ouaguenouni/Matrix-Studio-ESP32/cad/enclosure-comparison/01-line/exploded.png

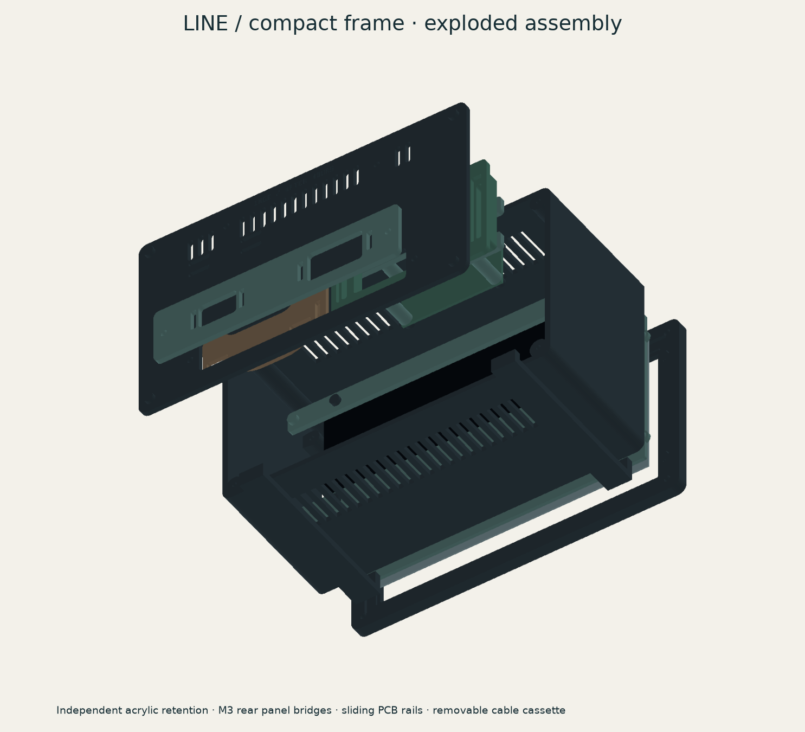
cad/enclosure-comparison/01-line/exploded.png
