ouaguenouni/Matrix-Studio-ESP32/cad/enclosure-comparison/03-gallery/exploded.png

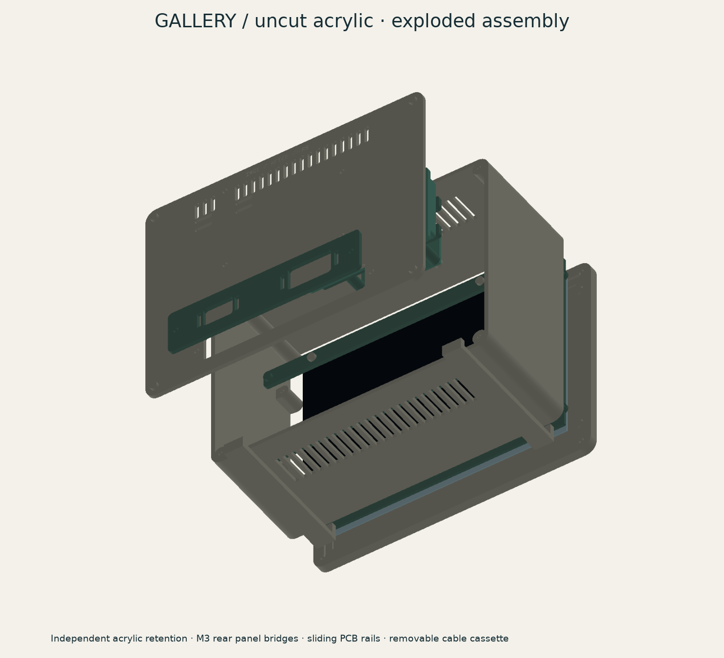
cad/enclosure-comparison/03-gallery/exploded.png
