ouaguenouni/Matrix-Studio-ESP32/cad/enclosure-comparison/04-vault/exploded.png

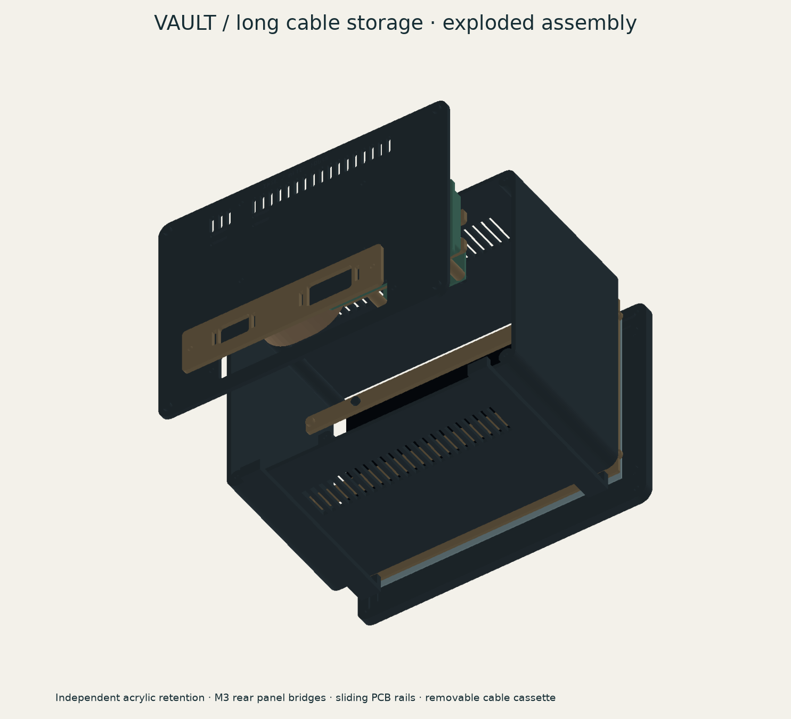
cad/enclosure-comparison/04-vault/exploded.png
