ouaguenouni/Matrix-Studio-ESP32/cad/enclosure-comparison/04-vault/preview.png

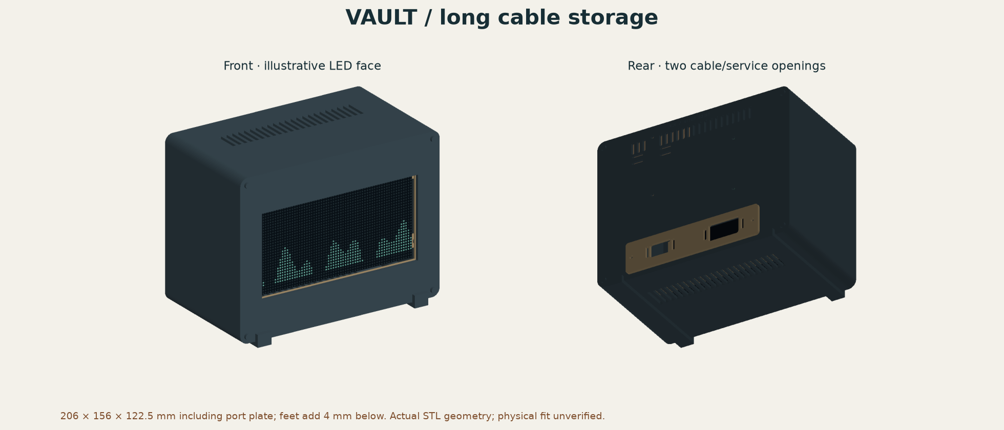
cad/enclosure-comparison/04-vault/preview.png
