ouaguenouni/Matrix-Studio-ESP32/cad/enclosure-comparison/vault-service.png

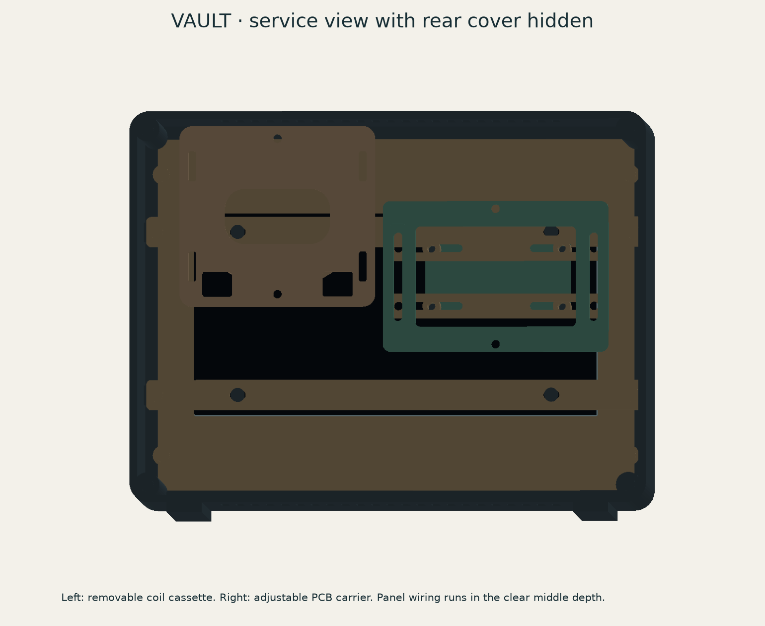
cad/enclosure-comparison/vault-service.png
