ouaguenouni/Matrix-Studio-ESP32/pictures/IMG_20261005_003129984.jpg

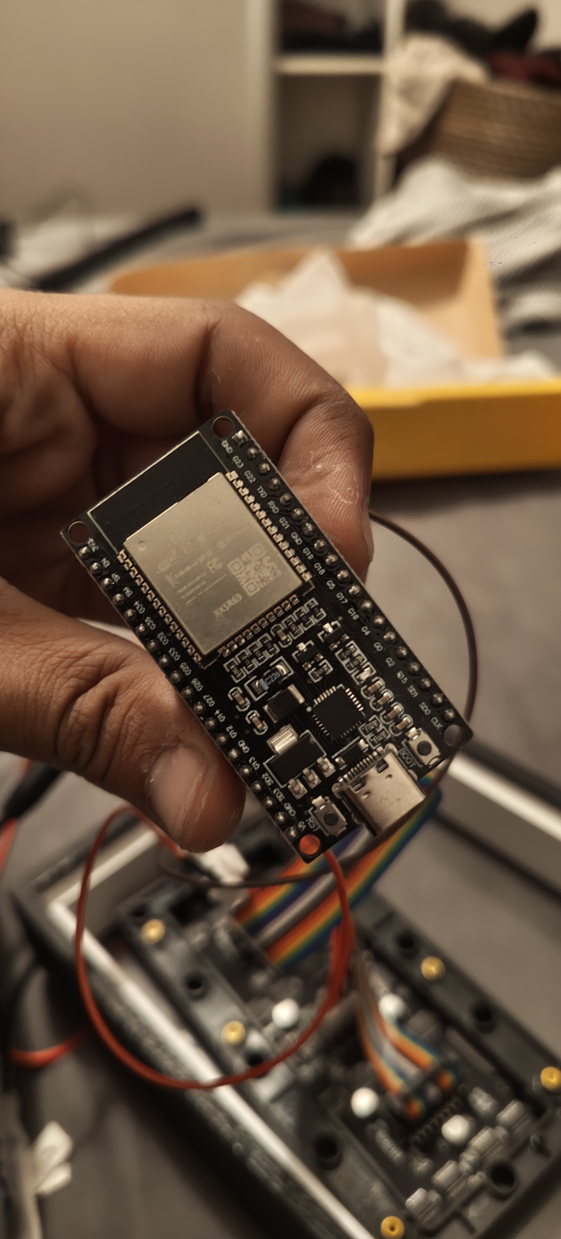
pictures/IMG_20261005_003129984.jpg
