ouaguenouni/Matrix-Studio-ESP32/pictures/IMG_20261005_003135957.jpg

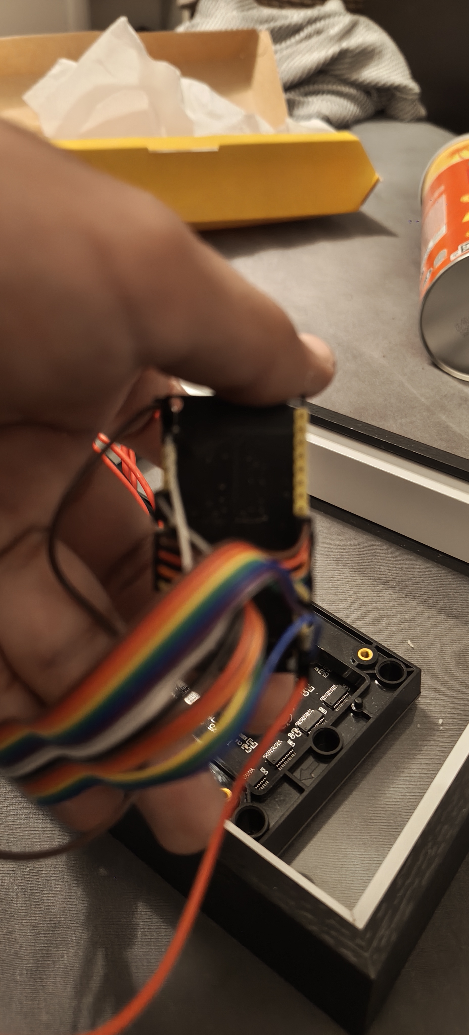
pictures/IMG_20261005_003135957.jpg
