ouaguenouni/Matrix-Studio-ESP32/pictures/IMG_20261005_003139460.jpg

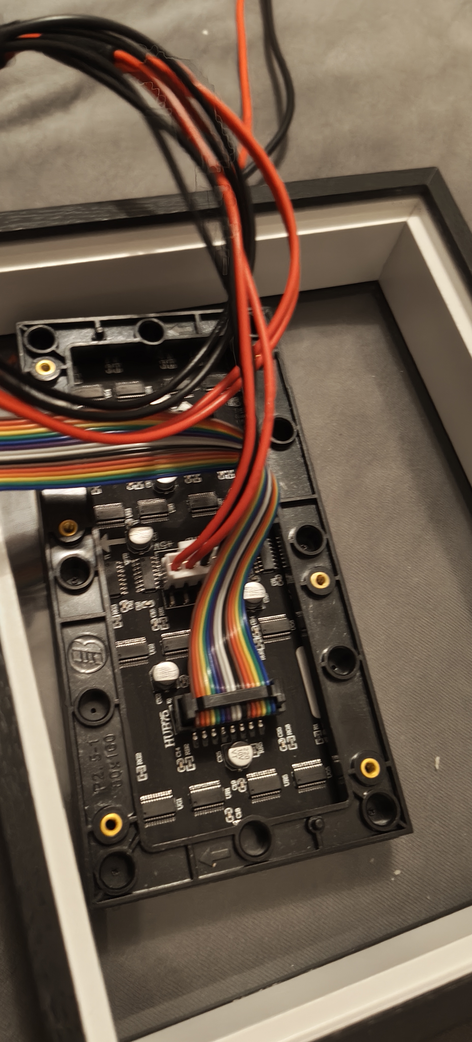
pictures/IMG_20261005_003139460.jpg
