ouaguenouni/Matrix-Studio-ESP32/pictures/IMG_20261005_003144986.jpg

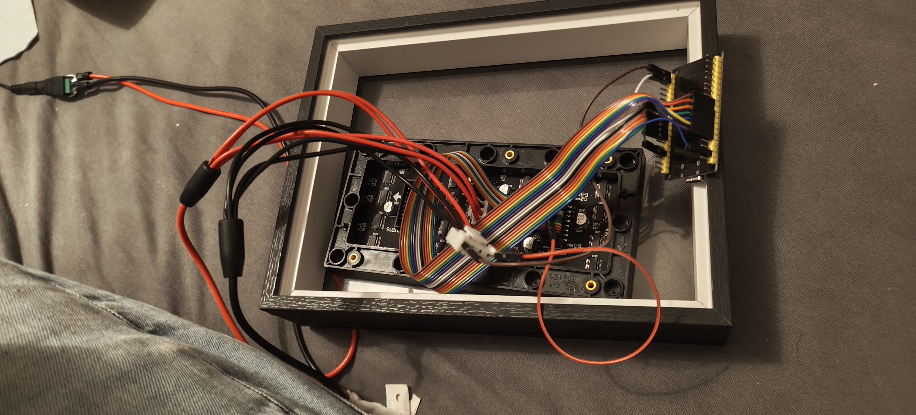
pictures/IMG_20261005_003144986.jpg
