ouaguenouni/Matrix-Studio-ESP32/pictures/IMG_20261005_003153289.jpg

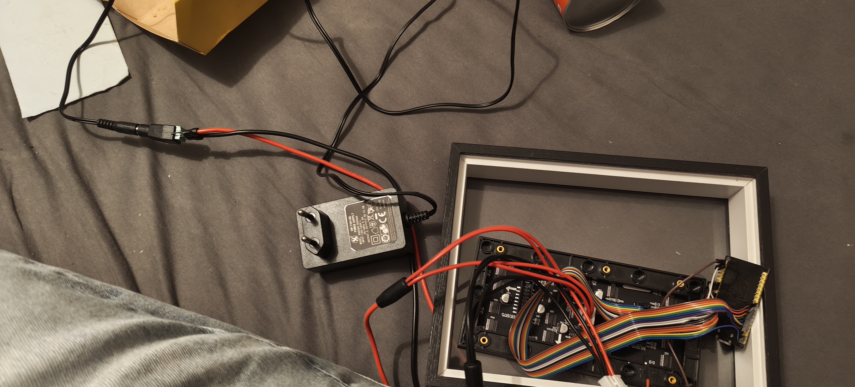
pictures/IMG_20261005_003153289.jpg
