ouaguenouni/Matrix-Studio-ESP32/cad/enclosure-comparison/01-line/stl/carrier.stl

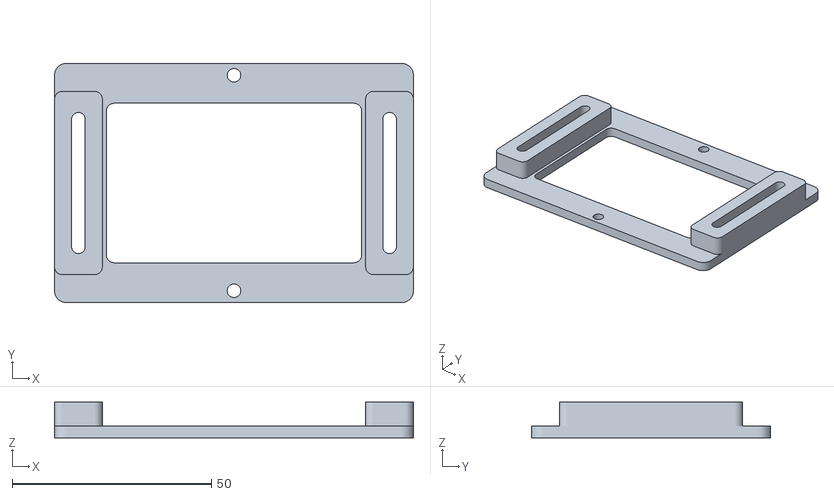
[picture p32: CAD file, 2026-10-05]
cad/enclosure-comparison/01-line/stl/carrier.stl
90.0 x 60.0 x 9.00
