ouaguenouni/Matrix-Studio-ESP32/cad/enclosure-comparison/03-gallery/stl/body.stl

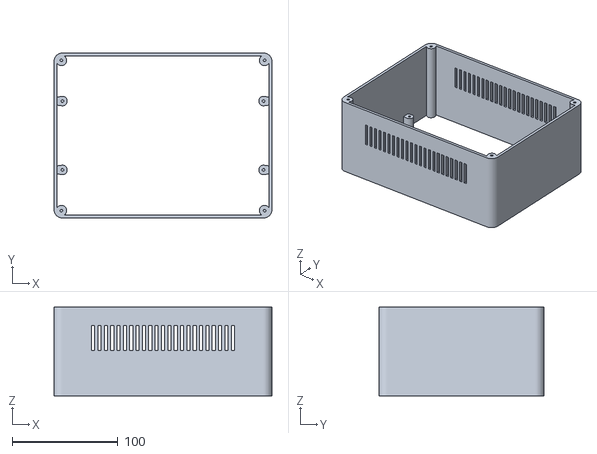
[picture p33: CAD file, 2026-10-05]
cad/enclosure-comparison/03-gallery/stl/body.stl
206.0 x 156.0 x 84.0
