ouaguenouni/Matrix-Studio-ESP32/cad/enclosure-comparison/04-vault/stl/body.stl

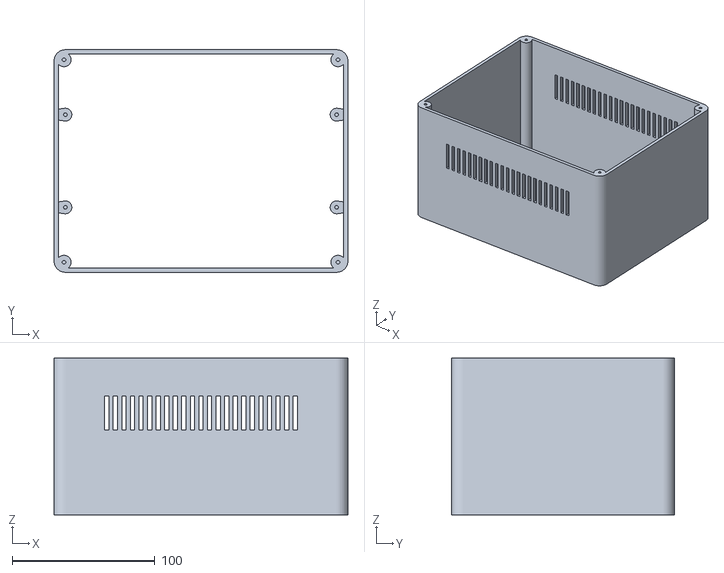
[picture p34: CAD file, 2026-10-05]
cad/enclosure-comparison/04-vault/stl/body.stl
206.0 x 156.0 x 110.0
