ouaguenouni/Matrix-Studio-ESP32/cad/enclosure-comparison/05-console/stl/keeper.stl

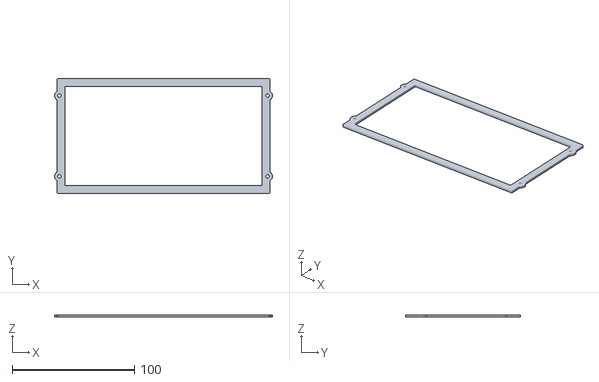
[picture p35: CAD file, 2026-10-05]
cad/enclosure-comparison/05-console/stl/keeper.stl
178.0 x 94.0 x 2.00
