ouaguenouni/Matrix-Studio-ESP32/cad/inge-after-hours/prototype-stl/lid.stl

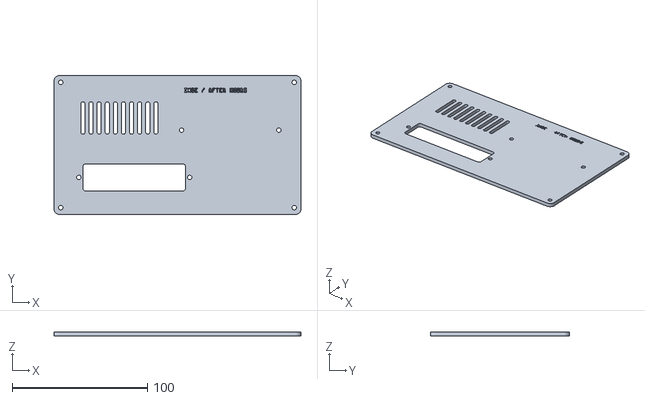
[picture p36: CAD file, 2026-10-05]
cad/inge-after-hours/prototype-stl/lid.stl
182.8 x 102.8 x 3.00
