ouaguenouni/Matrix-Studio-ESP32/cad/minimal-frame/reference/power_mock.stl

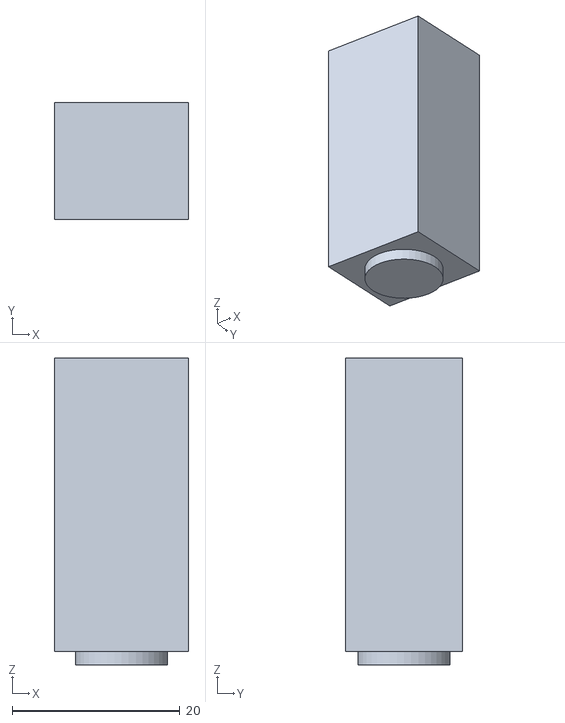
[picture p37: CAD file, 2026-10-05]
cad/minimal-frame/reference/power_mock.stl
16.0 x 14.0 x 36.6
