ouaguenouni/Matrix-Studio-ESP32/cad/enclosure-comparison/01-line/stl/ports.stl

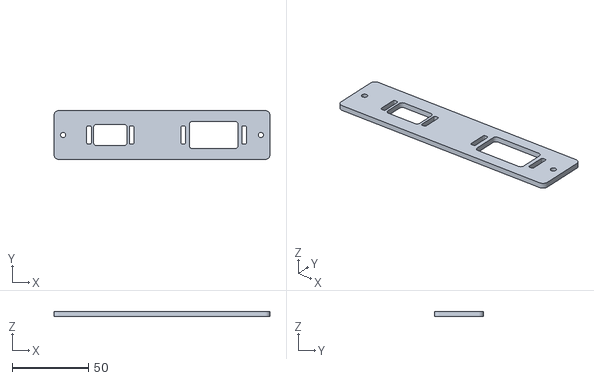
[picture p38: CAD file, 2026-10-05]
cad/enclosure-comparison/01-line/stl/ports.stl
142.0 x 32.0 x 3.00
