ouaguenouni/Matrix-Studio-ESP32/cad/enclosure-comparison/02-orbit/stl/spacer.stl

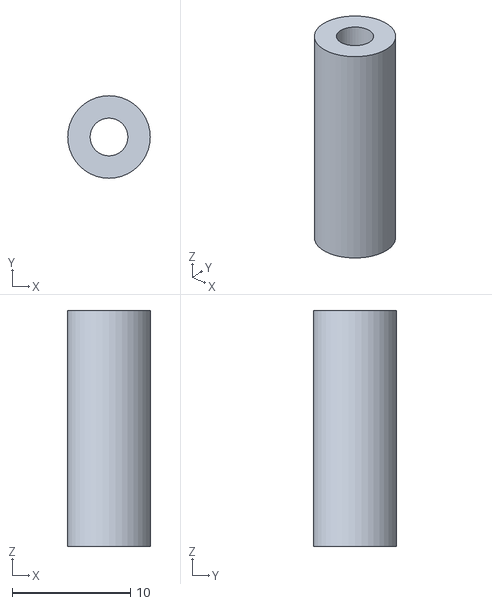
[picture p39: CAD file, 2026-10-05]
cad/enclosure-comparison/02-orbit/stl/spacer.stl
7.00 x 7.00 x 20.0
