ouaguenouni/Matrix-Studio-ESP32/cad/enclosure-comparison/03-gallery/stl/bridge.stl

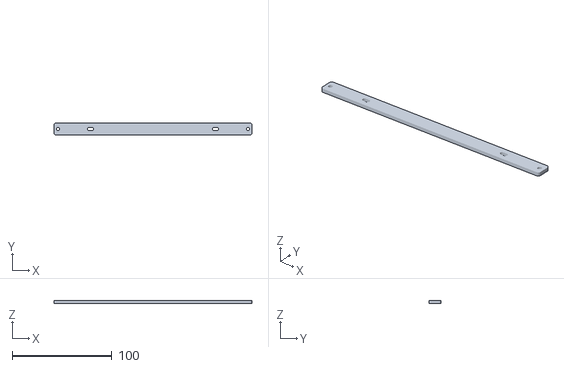
[picture p40: CAD file, 2026-10-05]
cad/enclosure-comparison/03-gallery/stl/bridge.stl
198.0 x 12.0 x 3.00
