ouaguenouni/Matrix-Studio-ESP32/cad/inge-after-hours/prototype-stl/carrier.stl

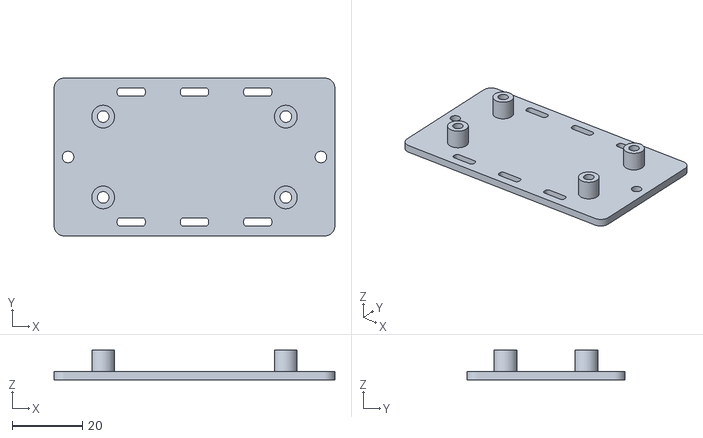
[picture p41: CAD file, 2026-10-05]
cad/inge-after-hours/prototype-stl/carrier.stl
80.0 x 45.0 x 8.40
