ouaguenouni/Matrix-Studio-ESP32/cad/minimal-frame/reference/usb_mock.stl

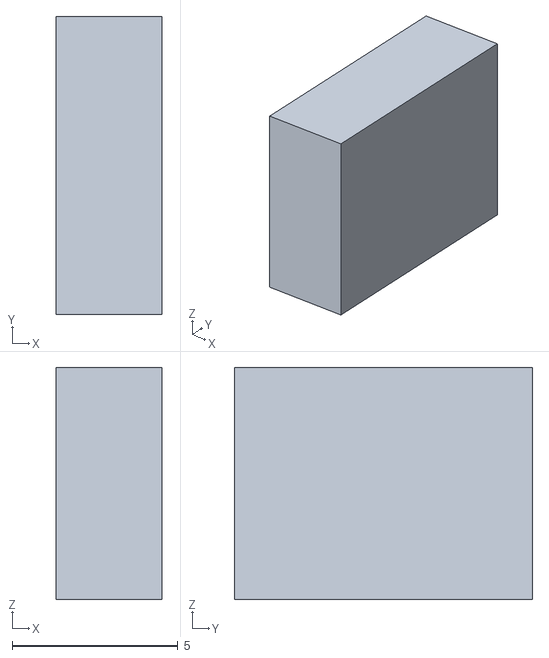
[picture p42: CAD file, 2026-10-05]
cad/minimal-frame/reference/usb_mock.stl
3.20 x 9.00 x 7.00
