ouaguenouni/Matrix-Studio-ESP32/cad/enclosure-comparison/01-line/stl/rail.stl

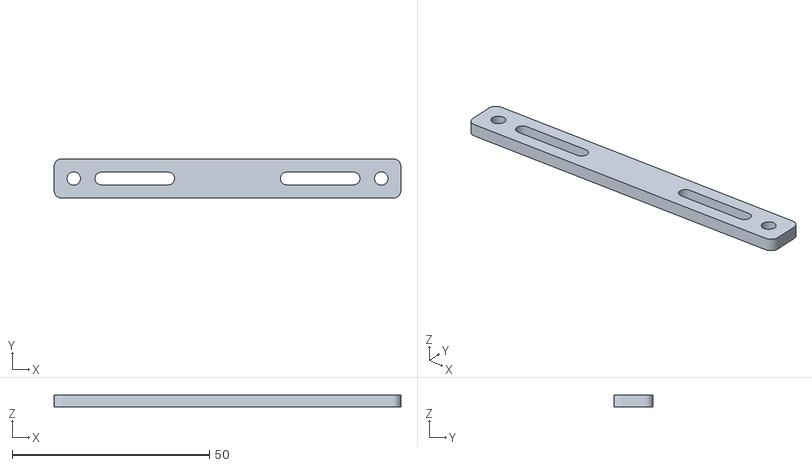
[picture p43: CAD file, 2026-10-05]
cad/enclosure-comparison/01-line/stl/rail.stl
88.0 x 10.0 x 3.00
