ouaguenouni/Matrix-Studio-ESP32/cad/enclosure-comparison/02-orbit/stl/body.stl

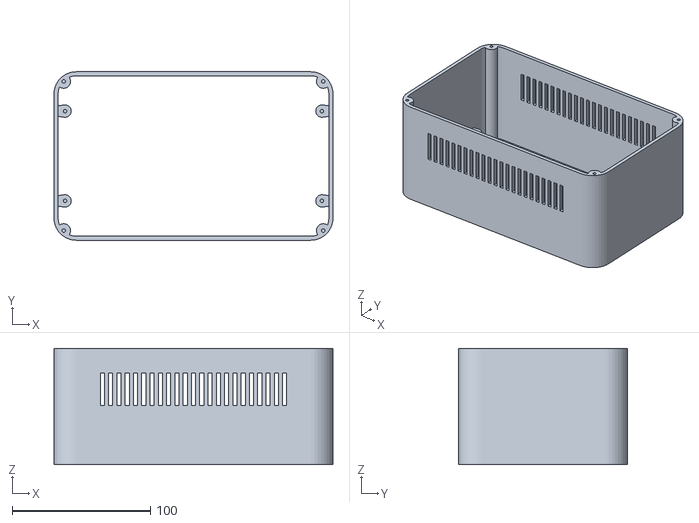
[picture p44: CAD file, 2026-10-05]
cad/enclosure-comparison/02-orbit/stl/body.stl
202.0 x 122.0 x 84.0
