ouaguenouni/Matrix-Studio-ESP32/cad/enclosure-comparison/03-gallery/stl/keeper.stl

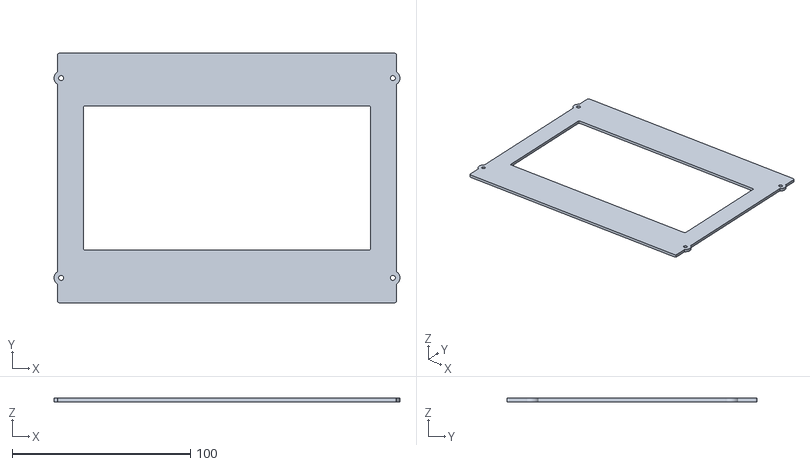
[picture p45: CAD file, 2026-10-05]
cad/enclosure-comparison/03-gallery/stl/keeper.stl
194.0 x 140.0 x 2.00
