ouaguenouni/Matrix-Studio-ESP32/cad/enclosure-comparison/04-vault/stl/feet.stl

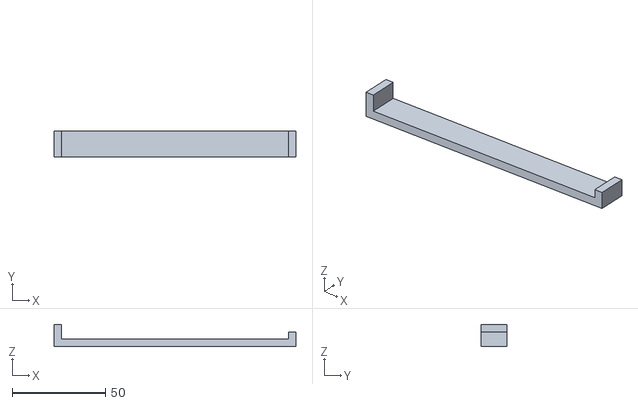
[picture p46: CAD file, 2026-10-05]
cad/enclosure-comparison/04-vault/stl/feet.stl
129.5 x 14.0 x 12.0
