ouaguenouni/Matrix-Studio-ESP32/cad/inge-after-hours/prototype-stl/stand.stl

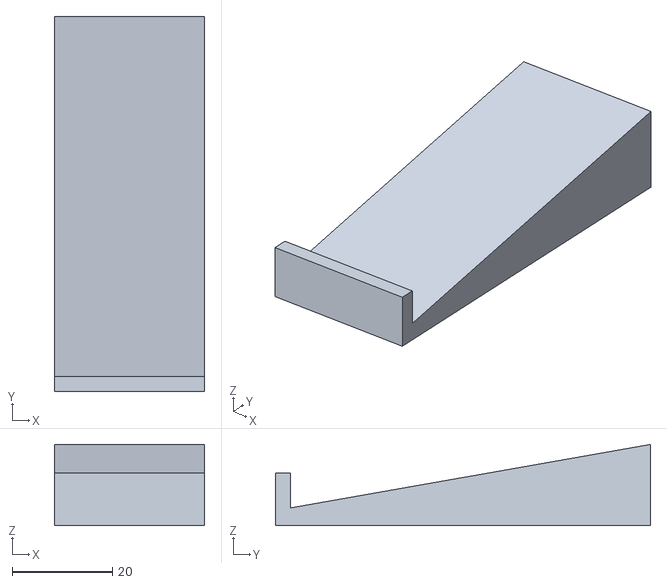
[picture p47: CAD file, 2026-10-05]
cad/inge-after-hours/prototype-stl/stand.stl
30.0 x 75.0 x 16.2
