ouaguenouni/Matrix-Studio-ESP32/cad/enclosure-comparison/02-orbit/stl/cassette.stl

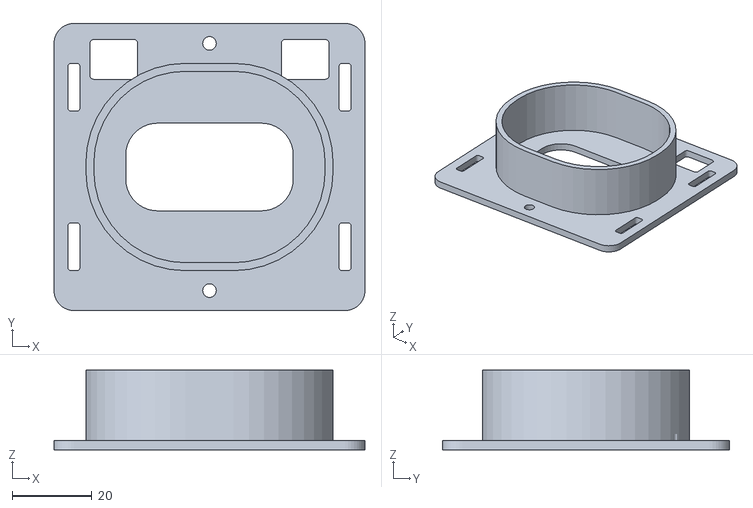
[picture p48: CAD file, 2026-10-05]
cad/enclosure-comparison/02-orbit/stl/cassette.stl
78.0 x 72.0 x 20.0
