ouaguenouni/Matrix-Studio-ESP32/cad/enclosure-comparison/03-gallery/stl/ports_usb_c.stl

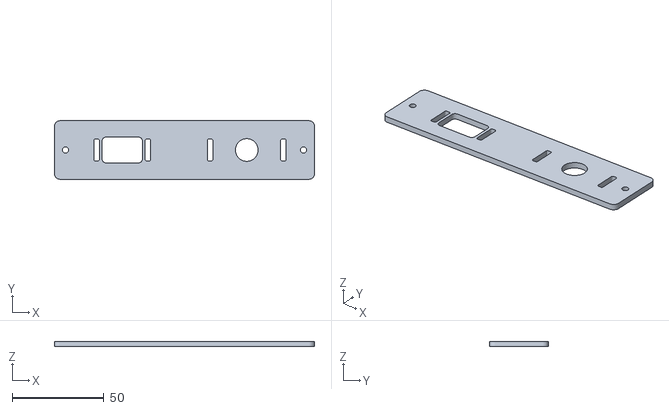
[picture p49: CAD file, 2026-10-05]
cad/enclosure-comparison/03-gallery/stl/ports_usb_c.stl
142.0 x 32.0 x 3.00
