ouaguenouni/Matrix-Studio-ESP32/cad/inge-after-hours/prototype-stl/front_spacer.stl

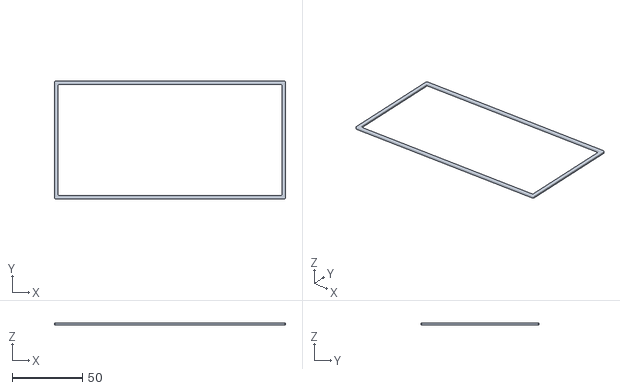
[picture p50: CAD file, 2026-10-05]
cad/inge-after-hours/prototype-stl/front_spacer.stl
164.0 x 84.0 x 1.50
