ouaguenouni/Matrix-Studio-ESP32/cad/enclosure-comparison/01-line/stl/body.stl

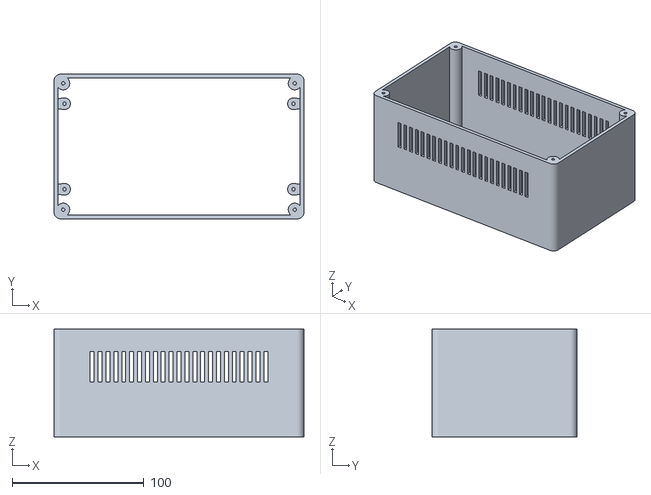
[picture p51: CAD file, 2026-10-05]
cad/enclosure-comparison/01-line/stl/body.stl
190.0 x 110.0 x 82.0
