ouaguenouni/Matrix-Studio-ESP32/cad/inge-after-hours/prototype-stl/clip.stl

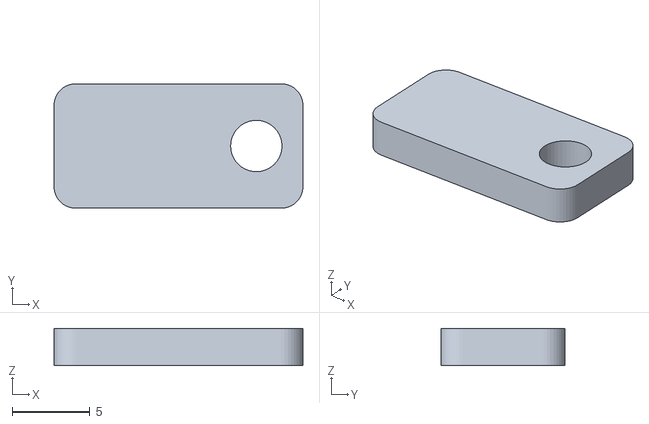
[picture p52: CAD file, 2026-10-05]
cad/inge-after-hours/prototype-stl/clip.stl
16.0 x 8.00 x 2.40
