ouaguenouni/Matrix-Studio-ESP32/cad/enclosure-comparison/03-gallery/stl/lid.stl

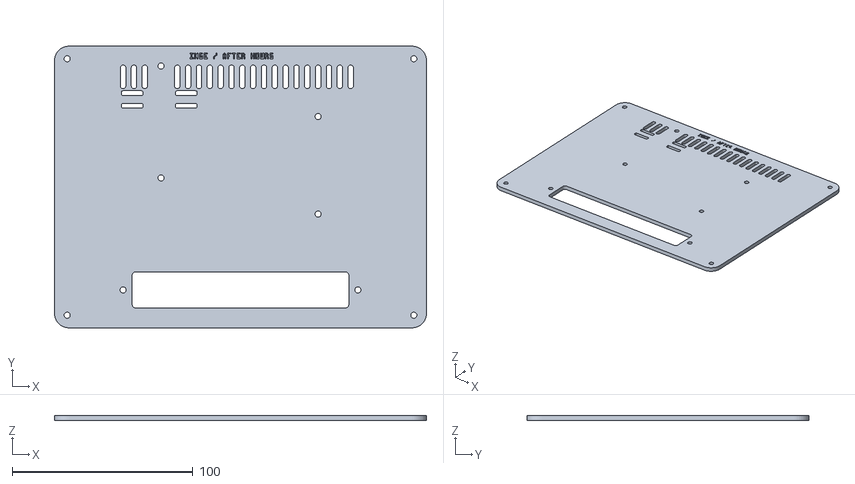
[picture p53: CAD file, 2026-10-05]
cad/enclosure-comparison/03-gallery/stl/lid.stl
206.0 x 156.0 x 3.00
