ouaguenouni/Matrix-Studio-ESP32/cad/enclosure-comparison/04-vault/stl/cassette.stl

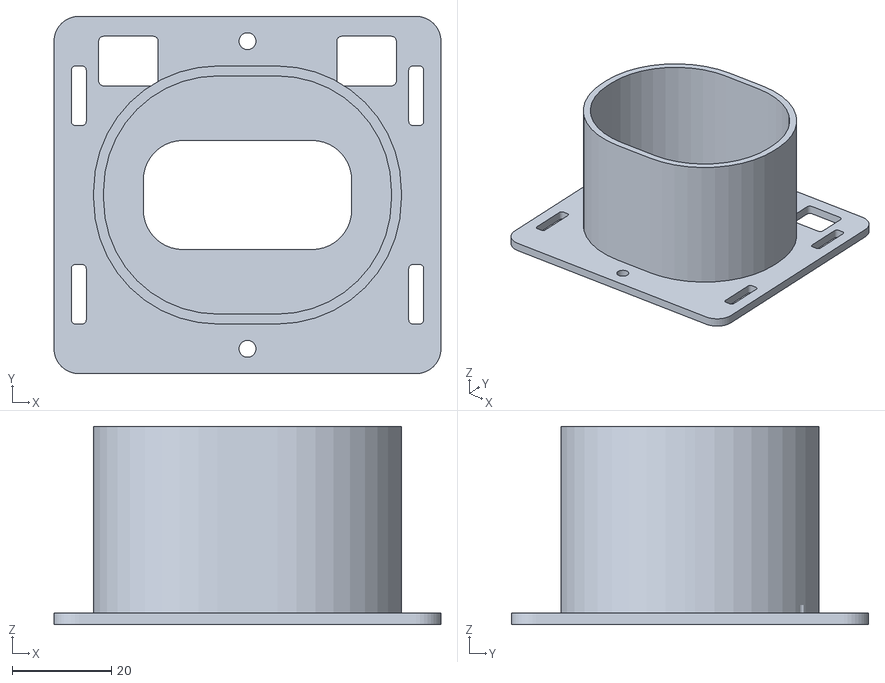
[picture p54: CAD file, 2026-10-05]
cad/enclosure-comparison/04-vault/stl/cassette.stl
78.0 x 72.0 x 40.0
