ouaguenouni/Matrix-Studio-ESP32/cad/enclosure-comparison/05-console/stl/body.stl

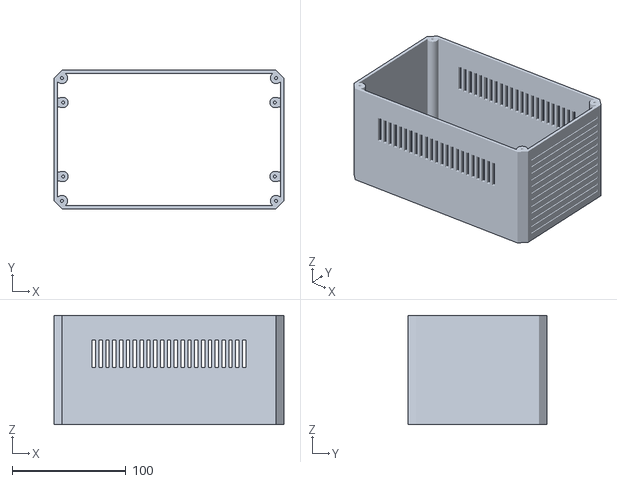
[picture p55: CAD file, 2026-10-05]
cad/enclosure-comparison/05-console/stl/body.stl
202.0 x 122.0 x 96.0
