ouaguenouni/Matrix-Studio-ESP32/cad/inge-after-hours/prototype-stl/ports.stl

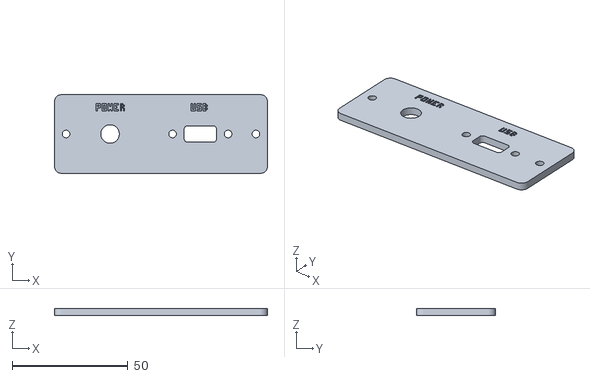
[picture p56: CAD file, 2026-10-05]
cad/inge-after-hours/prototype-stl/ports.stl
92.0 x 34.0 x 3.00
