ouaguenouni/Matrix-Studio-ESP32/cad/enclosure-comparison/01-line/stl/cassette.stl

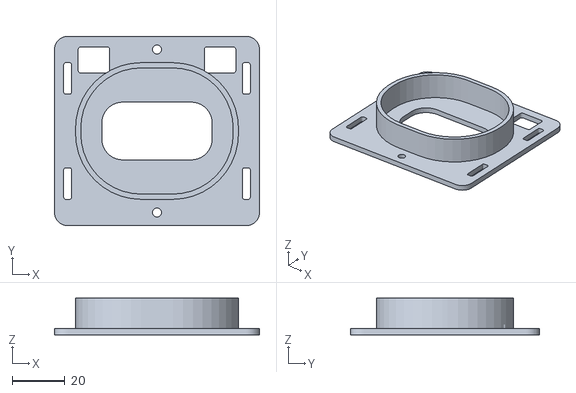
[picture p57: CAD file, 2026-10-05]
cad/enclosure-comparison/01-line/stl/cassette.stl
78.0 x 72.0 x 14.0
