ouaguenouni/Matrix-Studio-ESP32/cad/enclosure-comparison/05-console/stl/cassette.stl

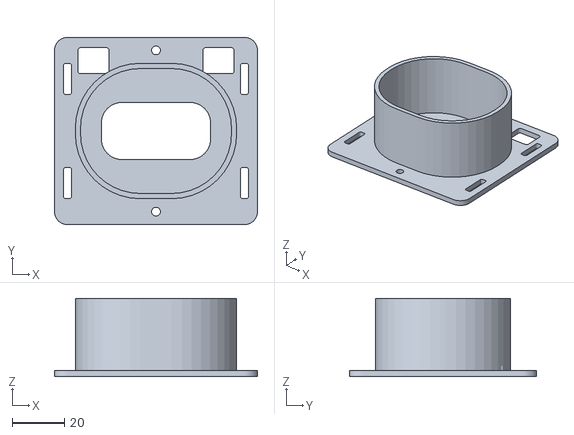
[picture p58: CAD file, 2026-10-05]
cad/enclosure-comparison/05-console/stl/cassette.stl
78.0 x 72.0 x 30.0
