ouaguenouni/Matrix-Studio-ESP32/cad/enclosure-comparison/02-orbit/stl/lid.stl

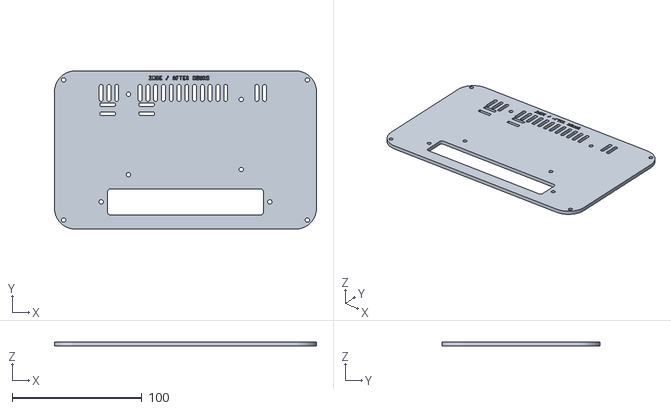
[picture p59: CAD file, 2026-10-05]
cad/enclosure-comparison/02-orbit/stl/lid.stl
202.0 x 122.0 x 3.00
