ouaguenouni/Matrix-Studio-ESP32/cad/enclosure-comparison/03-gallery/stl/feet.stl

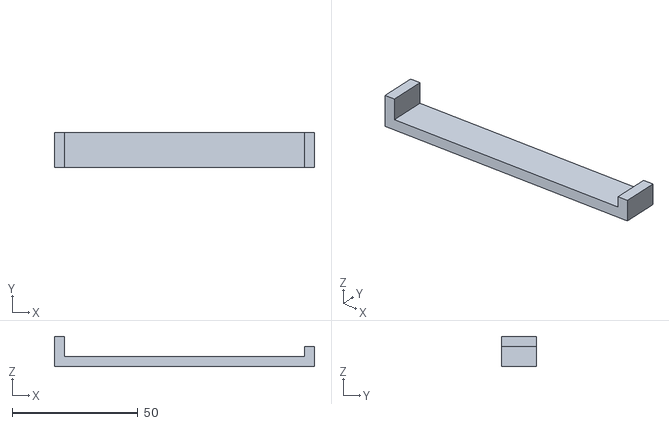
[picture p60: CAD file, 2026-10-05]
cad/enclosure-comparison/03-gallery/stl/feet.stl
103.5 x 14.0 x 12.0
