ouaguenouni/Matrix-Studio-ESP32/cad/enclosure-comparison/01-line/stl/lid.stl

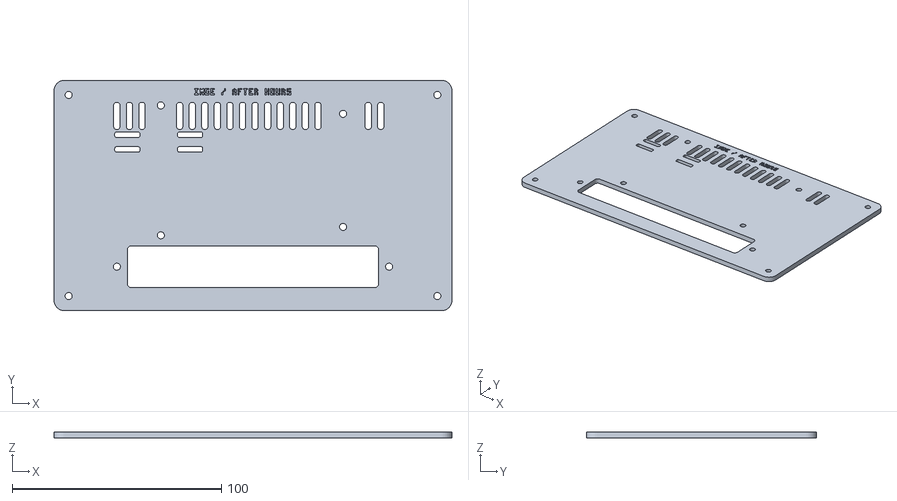
[picture p61: CAD file, 2026-10-05]
cad/enclosure-comparison/01-line/stl/lid.stl
190.0 x 110.0 x 3.00
