ouaguenouni/Matrix-Studio-ESP32/cad/enclosure-comparison/05-console/stl/bridge.stl

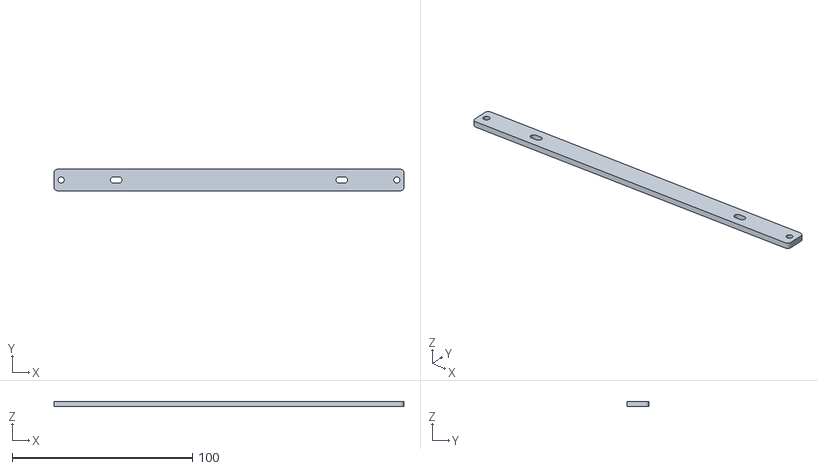
[picture p62: CAD file, 2026-10-05]
cad/enclosure-comparison/05-console/stl/bridge.stl
194.0 x 12.0 x 3.00
