ouaguenouni/Matrix-Studio-ESP32/cad/enclosure-comparison/01-line/stl/feet.stl

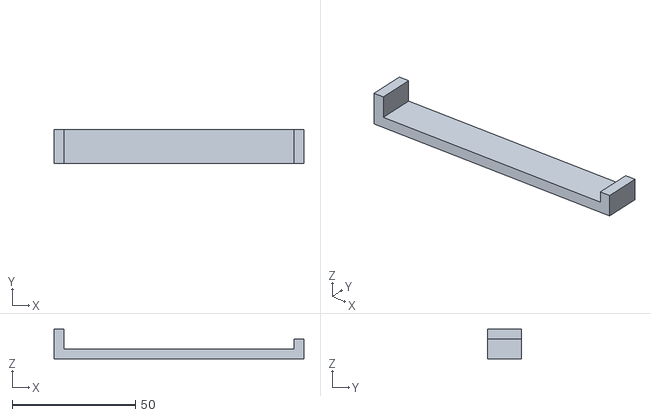
[picture p63: CAD file, 2026-10-05]
cad/enclosure-comparison/01-line/stl/feet.stl
101.5 x 14.0 x 12.0
