ouaguenouni/Matrix-Studio-ESP32/cad/enclosure-comparison/05-console/stl/lid.stl

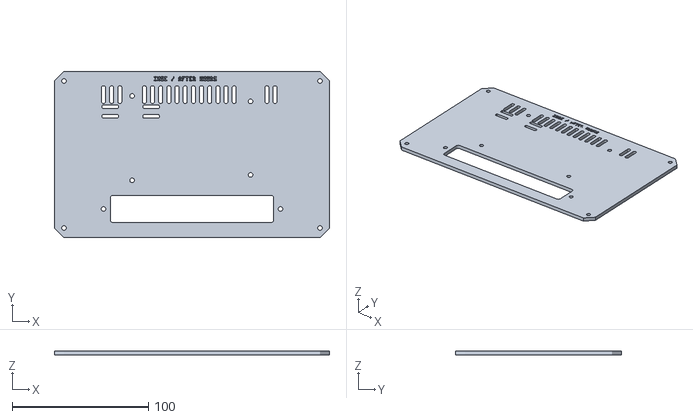
[picture p64: CAD file, 2026-10-05]
cad/enclosure-comparison/05-console/stl/lid.stl
202.0 x 122.0 x 3.00
