ouaguenouni/Matrix-Studio-ESP32/cad/enclosure-comparison/01-line/stl/bridge.stl

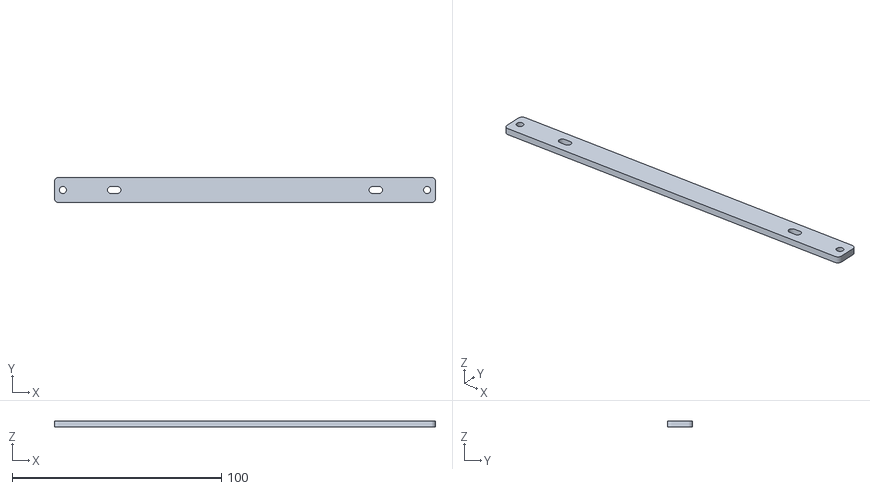
[picture p65: CAD file, 2026-10-05]
cad/enclosure-comparison/01-line/stl/bridge.stl
182.0 x 12.0 x 3.00
