ouaguenouni/Matrix-Studio-ESP32/cad/enclosure-comparison/05-console/stl/feet.stl

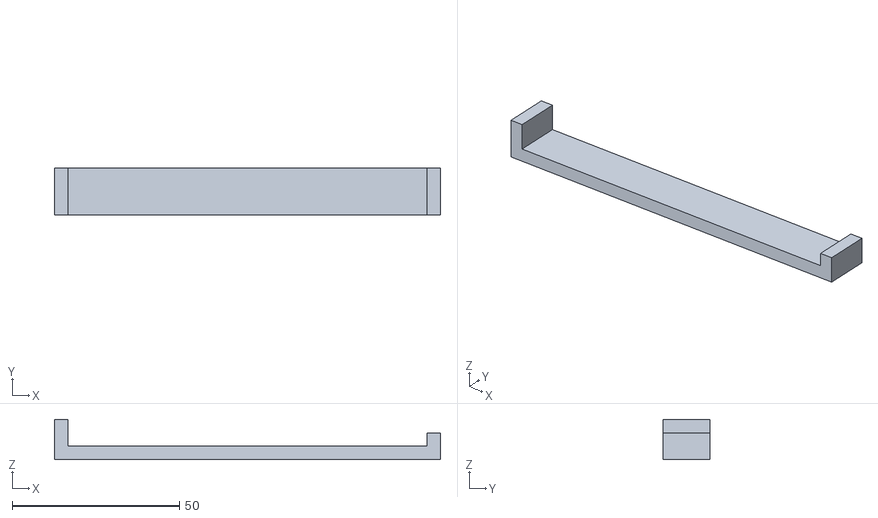
[picture p66: CAD file, 2026-10-05]
cad/enclosure-comparison/05-console/stl/feet.stl
115.5 x 14.0 x 12.0
