ouaguenouni/Matrix-Studio-ESP32/cad/enclosure-comparison/01-line/model.scad

// Set part in Customizer; see ../PRINT-GUIDE.md
style_id = 1;
include <../family.scad>
panel_depth = 14.5;
acrylic_thickness = 1.0;
pcb_length = 58.0;
pcb_width = 29.0;
pcb_thickness = 1.6;
pcb_hole_length = 52.0;
pcb_hole_width = 23.0;
pcb_standoff = 20.0;
