ouaguenouni/Matrix-Studio-ESP32/cad/inge-after-hours/assembled-preview.png

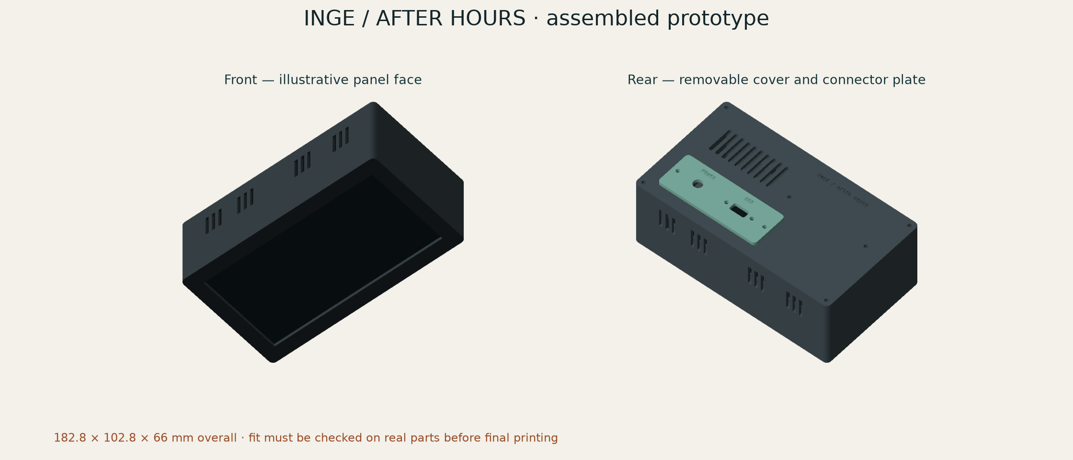
cad/inge-after-hours/assembled-preview.png
